DavesKosmoModules/Rain-Noise/Docs/20211023_091420.jpg

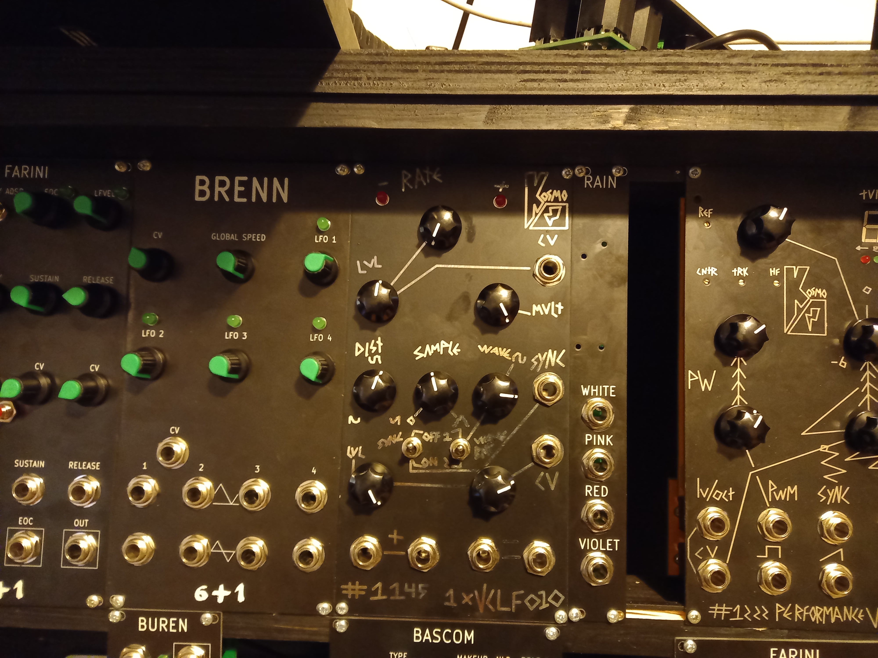
Docs/20211023_091420.jpg
